BwanaFr/UPS-SNMP/hardware/PCB/esp32-ups-snmp/3D/Wurth_614004134726 (rev1).stp

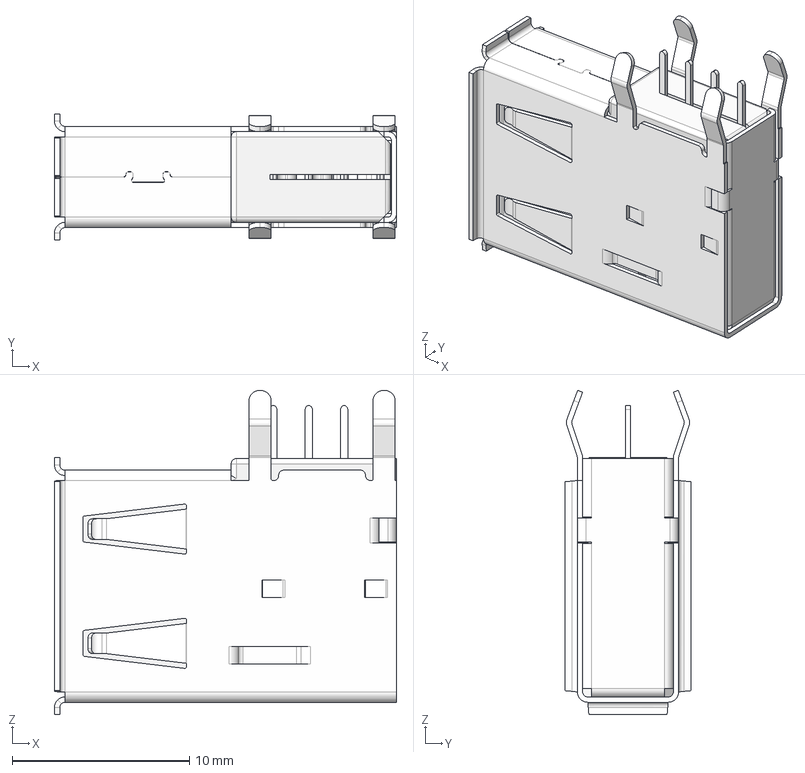
[picture p15: CAD file, 2026-03-25]
hardware/PCB/esp32-ups-snmp/3D/Wurth_614004134726 (rev1).stp
19.3 x 7.10 x 18.3 mm
Blech
Blech_Deckel
Pin_4
Gehäuse_Pin
Pin_3
Pin_2
Pin_1
