BwanaFr/UPS-SNMP/hardware/PCB/esp32-ups-snmp/3D/S05B-ZESK-2D.STEP

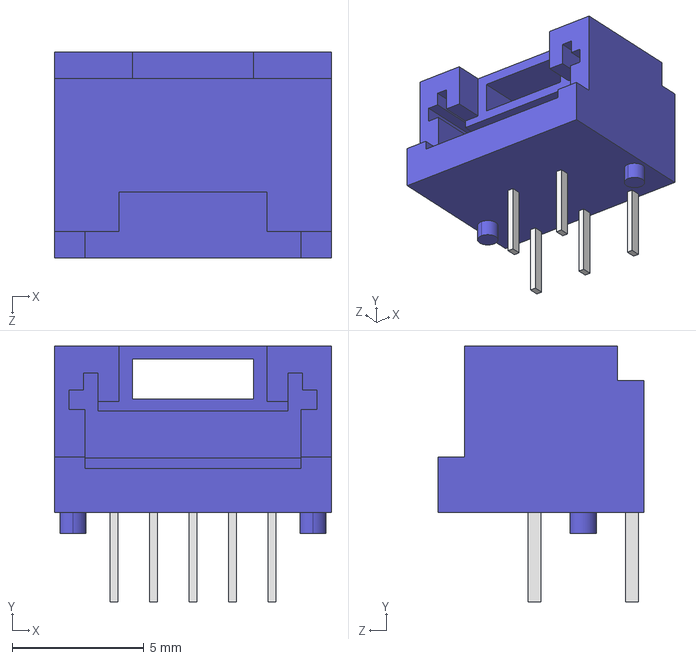
[picture p16: CAD file, 2026-03-25]
hardware/PCB/esp32-ups-snmp/3D/S05B-ZESK-2D.STEP
10.5 x 9.70 x 7.80 mm
