BwanaFr/UPS-SNMP/hardware/PCB/esp32-ups-snmp/3D/WaveshareETH/SSQ-106-03-L-S.stp

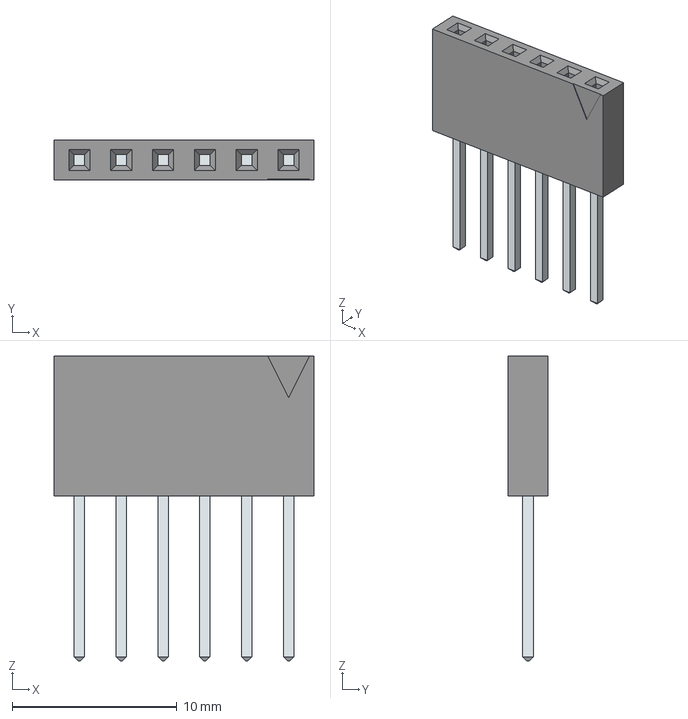
[picture p17: CAD file, 2026-03-25]
hardware/PCB/esp32-ups-snmp/3D/WaveshareETH/SSQ-106-03-L-S.stp
15.8 x 2.41 x 18.5 mm
LeadsArray
