BwanaFr/UPS-SNMP/hardware/PCB/esp32-ups-snmp/3D/WaveshareETH/ESQ-106-12-L-S.stp

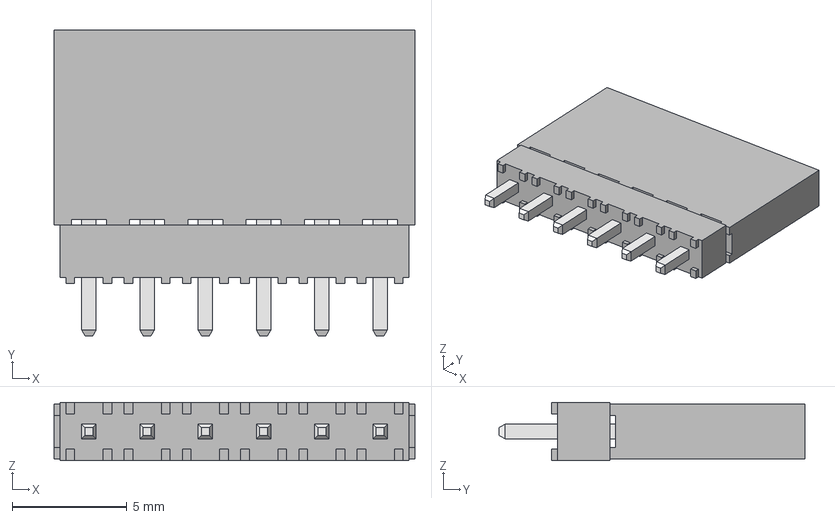
[picture p18: CAD file, 2026-03-25]
hardware/PCB/esp32-ups-snmp/3D/WaveshareETH/ESQ-106-12-L-S.stp
15.7 x 13.3 x 2.54 mm
ESQ-106-12-L-S_socket
ESQ-106-12-L-S_pins
ESQ-106-12-L-S2_pins
ESQ-106-12-G-S-LL_bpins
