BwanaFr/UPS-SNMP/hardware/PCB/esp32-ups-snmp/3D/WaveshareETH/D8_H6.2_v2.step

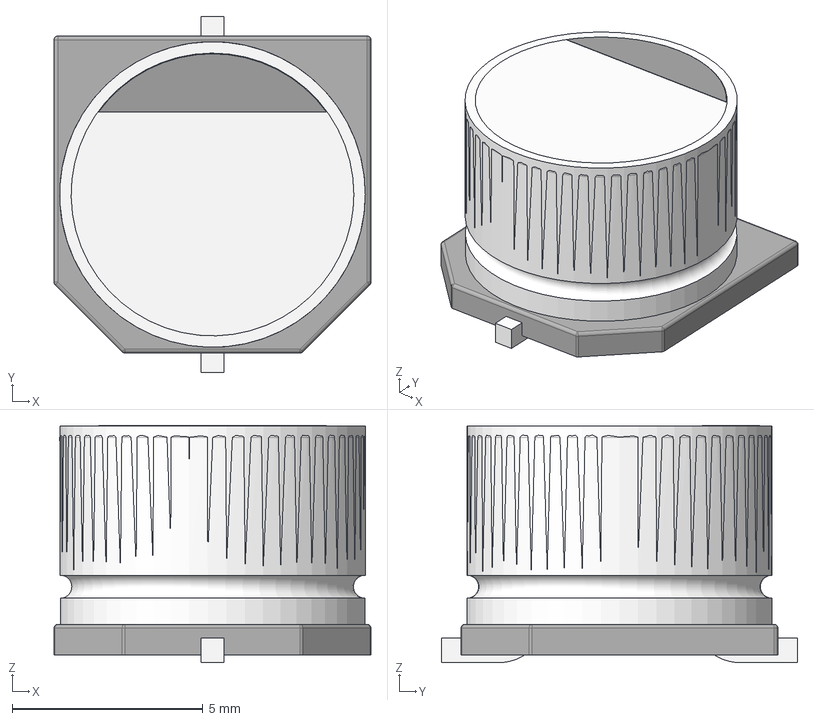
[picture p19: CAD file, 2026-03-25]
hardware/PCB/esp32-ups-snmp/3D/WaveshareETH/D8_H6.2_v2.step
8.30 x 9.33 x 6.21 mm
Pins
Pins001
Socle
Mark
