BwanaFr/UPS-SNMP/hardware/PCB/esp32-ups-snmp/3D/WaveshareETH/pcb_connector_890-80-006-10-001101.stp

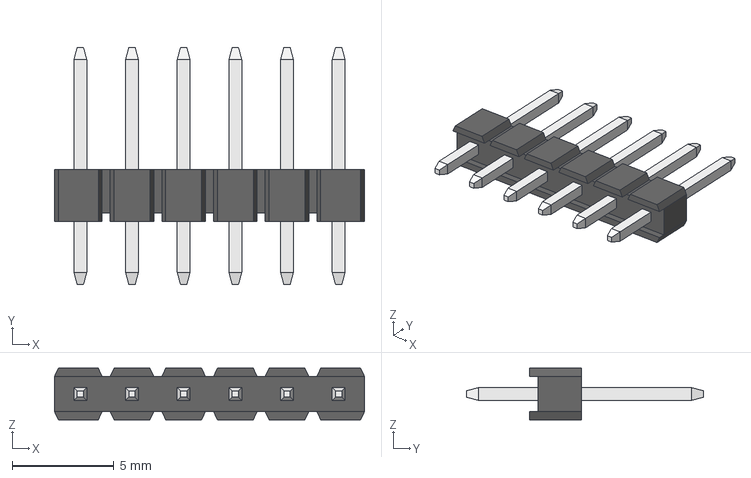
[picture p20: CAD file, 2026-03-25]
hardware/PCB/esp32-ups-snmp/3D/WaveshareETH/pcb_connector_890-80-006-10-001101.stp
15.2 x 11.6 x 2.54 mm
