BwanaFr/UPS-SNMP/hardware/PCB/esp32-ups-snmp/3D/WaveshareETH/c1210c107m9pactu.stp

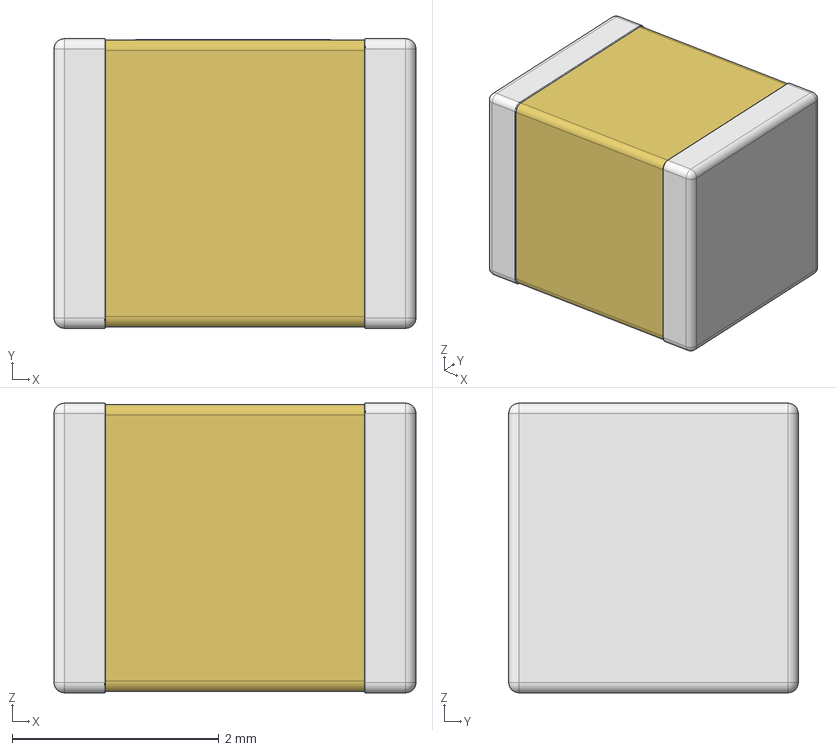
[picture p21: CAD file, 2026-03-25]
hardware/PCB/esp32-ups-snmp/3D/WaveshareETH/c1210c107m9pactu.stp
3.50 x 2.80 x 2.80 mm
