BwanaFr/UPS-SNMP/hardware/PCB/esp32-ups-snmp/3D/WaveshareETH/SOIC08 narrow.igs

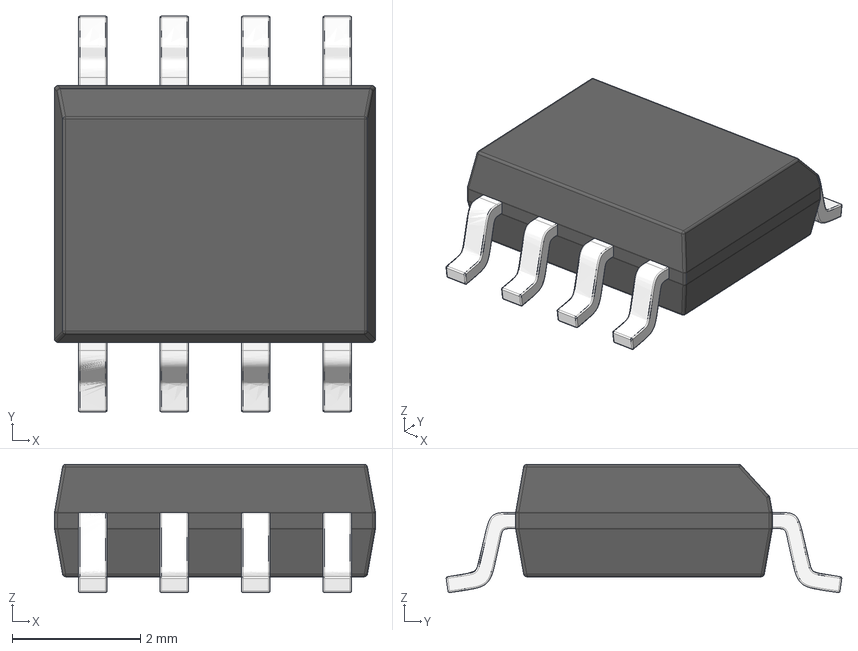
[picture p22: CAD file, 2026-03-25]
hardware/PCB/esp32-ups-snmp/3D/WaveshareETH/SOIC08 narrow.igs
5.00 x 6.16 x 2.00 mm
