BwanaFr/UPS-SNMP/firmware/production/src/Temperature.cpp

#include <Temperature.hpp>

#ifdef HAS_TEMP_PROBE
#include "esp_log.h"
#include <FreeRTOS.h>

static const char *TAG = "TempProbe";

#ifndef TEMP_PROBE_PIN
#define TEMP_PROBE_PIN 15
#endif

#ifndef TEMP_READ_PERIOD
#define TEMP_READ_PERIOD 500
#endif

#ifndef TEMP_FAILURE_MAX
#define TEMP_FAILURE_MAX 5
#endif

TemperatureProbe::TemperatureProbe(uint8_t pin) :
    wire_(pin), dallas_(&wire_), temperature_("Temperature", 0.0), StatusProvider("Probe", &temperature_), failureCount_(0)
{
}

void TemperatureProbe::begin()
{
    DeviceAddress sensorDeviceAddress;
    dallas_.begin();
    dallas_.getAddress(sensorDeviceAddress, 0);
    dallas_.setResolution(sensorDeviceAddress, 10);
    xTaskCreate(temperatureTask, "tempTask", 2048, (void*)this,  tskIDLE_PRIORITY + 1, NULL);
}

double TemperatureProbe::getTemperatureProbe()
{
    return temperature_.getValue();
}

void TemperatureProbe::readTemperature()
{
    for(;;){
        dallas_.requestTemperatures();
        float tempRead = dallas_.getTempCByIndex(0);
        if(tempRead == DEVICE_DISCONNECTED_C){
            if(failureCount_ < TEMP_FAILURE_MAX){
                ++failureCount_;
            }
        }else{
            failureCount_ = 0;
        }

        if(failureCount_ < TEMP_FAILURE_MAX){
            //Read ok
            temperature_.setValue(tempRead);
        }else{
            temperature_.setValue(DEVICE_DISCONNECTED_C);
        }

        delay(500);
    }
}

void TemperatureProbe::temperatureTask(void* param)
{
    TemperatureProbe* app = static_cast<TemperatureProbe*>(param);
    app->readTemperature();
}

TemperatureProbe tempProbe(TEMP_PROBE_PIN);

#endif
